ALLAN-mfQ/TrackBall_PC-GAME_Controller/+GYRO/WS000014.jpg

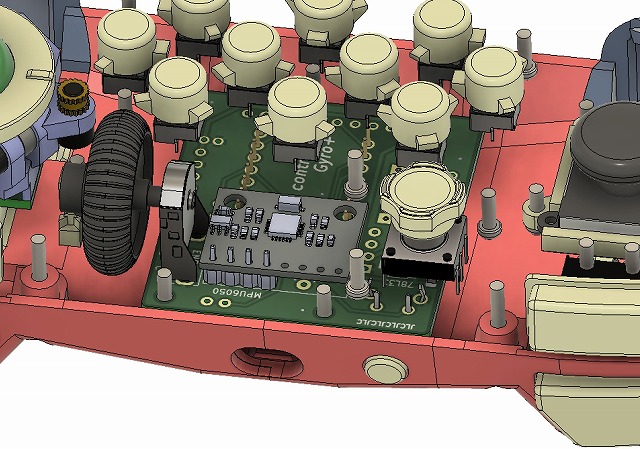
+GYRO/WS000014.jpg
