ALLAN-mfQ/TrackBall_PC-GAME_Controller/Gerber data/IMG/PCB3-2.jpg

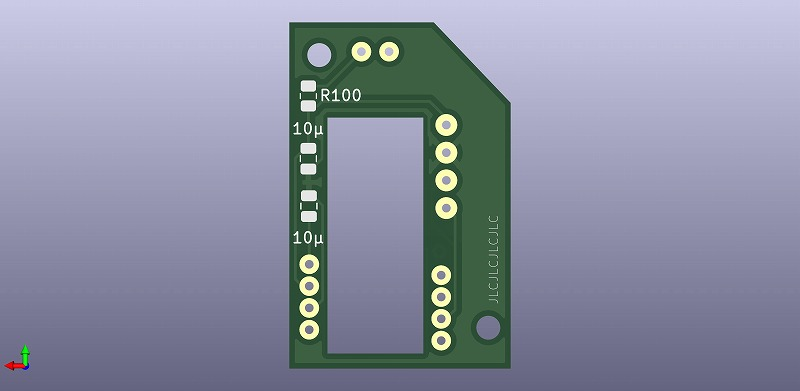
Gerber data/IMG/PCB3-2.jpg
