ALLAN-mfQ/TrackBall_PC-GAME_Controller/STL/button (10 pieces).stl

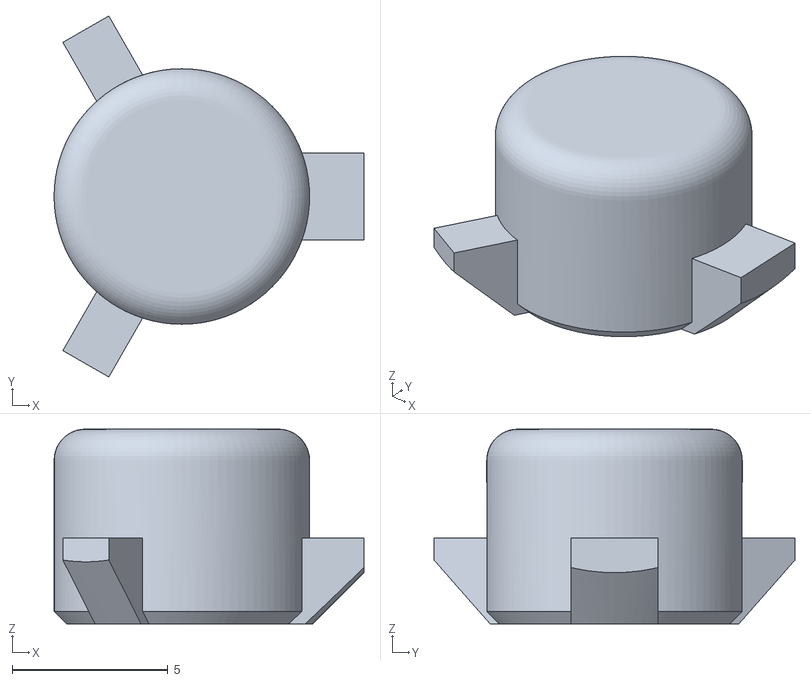
[picture p34: CAD file, 2022-09-13]
STL/button (10 pieces).stl
9.94 x 11.6 x 6.25
