ALLAN-mfQ/TrackBall_PC-GAME_Controller/STL/TB19mm mount Ring.stl

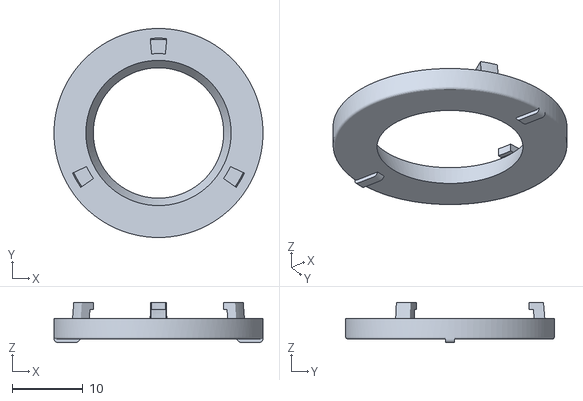
[picture p35: CAD file, 2022-09-13]
STL/TB19mm mount Ring.stl
29.6 x 29.6 x 5.68
